rbala25/shuffleboard/Firmware/src/sprites_bmp/background.bmp

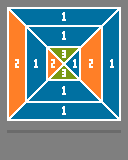
Firmware/src/sprites_bmp/background.bmp
