rbala25/shuffleboard/Firmware/src/Button.h

/* Button.h
 * Rising edge interrupts for PB4 (shoot) and PB1 (reset)
 */
#ifndef __BUTTON_H__
#define __BUTTON_H__

// Button_Init: configure PB4 and PB1 as rising-edge interrupt inputs
// Call after LaunchPad_Init, before __enable_irq
#ifdef __cplusplus
extern "C" {
#endif

void Button_Init(void);

#ifdef __cplusplus
}
#endif

#endif // __BUTTON_H__
